xventus/dectalk/src/src/S1V30120_init_data.h

/**
 * @file S1V30120_init_data.h
 * @author Petr Vanek (petr@fotoventus.cz)
 * @brief Initialization data for S1V30120
 * @version 0.1
 * @date 2022-08-29
 * 
 * @copyright Copyright (c) 2022 
 * 
 * Note: S1V30120 initialization data from https://global.epson.com/products_and_drivers/semicon/products/speech/voice/sla/s1v30120_init_data.html
 * The array of initialization values was created by converting the binary form from the Epson web pages. 
 * The rights and license are given in the link.
 * 
 */

#pragma once
#include <inttypes.h>
#include <pgmspace.h>

// array size is 31208
static const uint8_t S1V30120_INIT_DATA_ver2_1_6[] PROGMEM  = {
  0x18, 0xf0, 0x9f, 0xe5, 0x18, 0xf0, 0x9f, 0xe5, 0x18, 0xf0, 0x9f, 0xe5, 0x18, 0xf0, 0x9f, 0xe5, 
  0x18, 0xf0, 0x9f, 0xe5, 0x00, 0x00, 0xa0, 0xe1, 0x14, 0xf0, 0x9f, 0xe5, 0x14, 0xf0, 0x9f, 0xe5, 
  0x28, 0x01, 0xf0, 0xbf, 0x40, 0x02, 0xf0, 0xbf, 0x44, 0x02, 0xf0, 0xbf, 0x48, 0x02, 0xf0, 0xbf, 
  0x4c, 0x02, 0xf0, 0xbf, 0x50, 0x02, 0xf0, 0xbf, 0x54, 0x02, 0xf0, 0xbf, 0x00, 0x00, 0x00, 0x00, 
  0x08, 0x00, 0x9f, 0xe5, 0x08, 0x20, 0x9f, 0xe5, 0x00, 0x20, 0x82, 0xe0, 0x1e, 0xff, 0x2f, 0xe1, 
  0xf8, 0x7d, 0xf0, 0xbf, 0x78, 0x64, 0x01, 0x00, 0x24, 0x00, 0x9f, 0xe5, 0x00, 0x10, 0xa0, 0xe3, 
  0x00, 0x10, 0x80, 0xe5, 0xc0, 0x10, 0x80, 0xe5, 0x18, 0x10, 0x9f, 0xe5, 0x08, 0x10, 0x80, 0xe5, 
  0xff, 0x10, 0xa0, 0xe3, 0xc4, 0x10, 0x80, 0xe5, 0x00, 0x10, 0xa0, 0xe3, 0x10, 0x10, 0x80, 0xe5, 
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
  0x9a, 0x11, 0x04, 0xea, 0x78, 0x47, 0xc0, 0x46, 0x99, 0x11, 0x04, 0xea, 0x78, 0x47, 0xc0, 0x46, 
  0x71, 0x14, 0x00, 0xea, 0x71, 0x14, 0x00, 0xea, 0x6f, 0x14, 0x00, 0xea, 0x6f, 0xff, 0xff, 0xea, 
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
};
